DaqOpen/pqopen-device/docs/resources/assembly-step-3.jpg

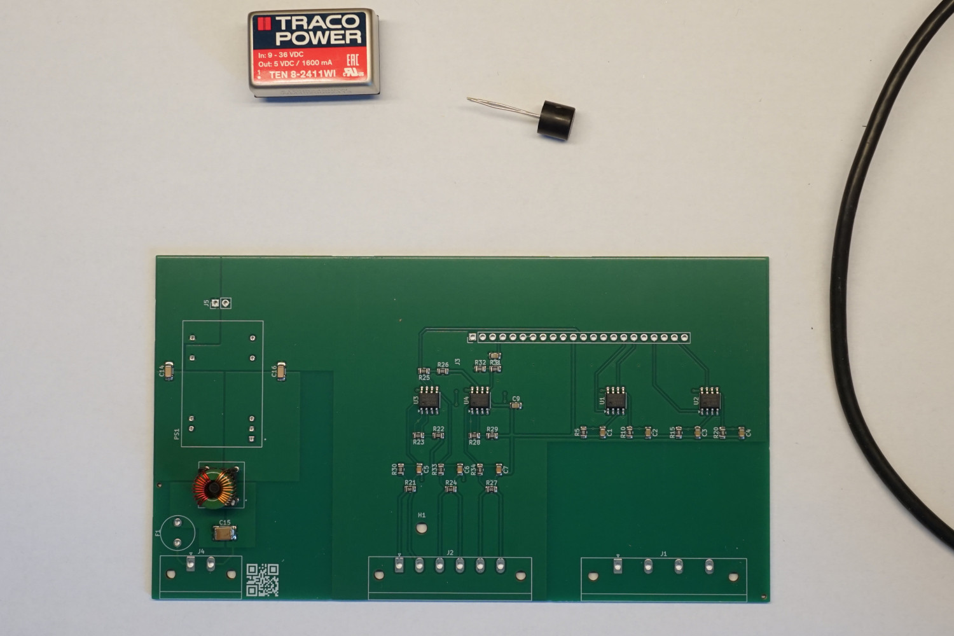
docs/resources/assembly-step-3.jpg
