DaqOpen/pqopen-device/docs/resources/assembly-step-4.jpg

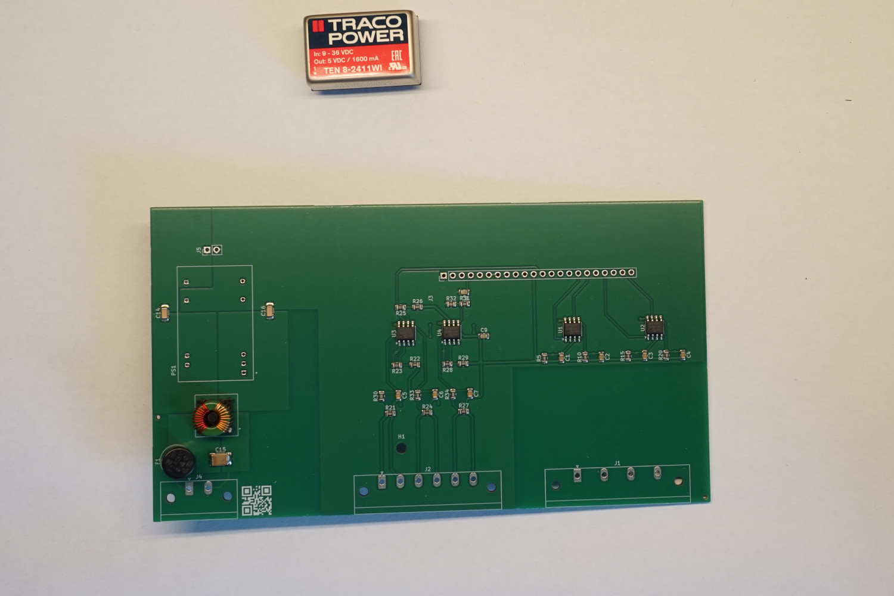
docs/resources/assembly-step-4.jpg
