DaqOpen/pqopen-device/docs/resources/assembly-step-5-1.jpg

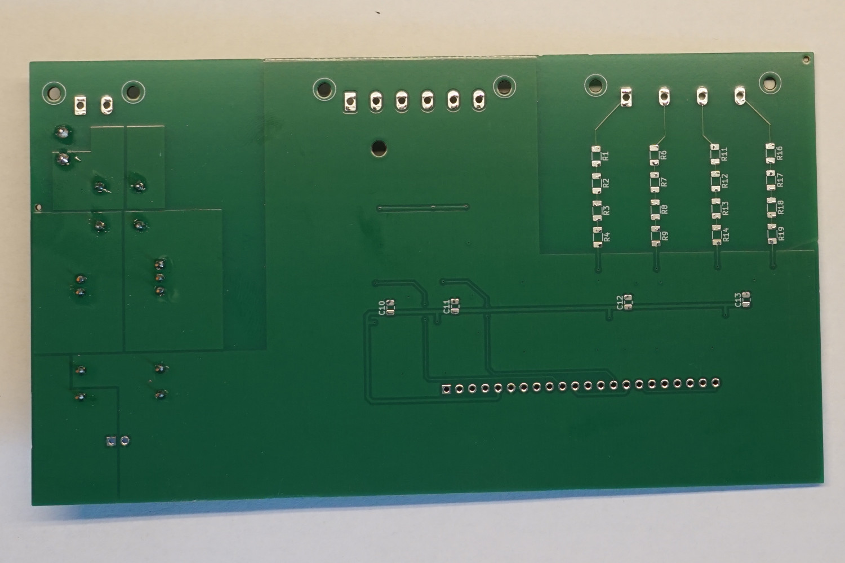
docs/resources/assembly-step-5-1.jpg
